bdini13/esp32-cc1101-multiband/output/placement-A2-top.png

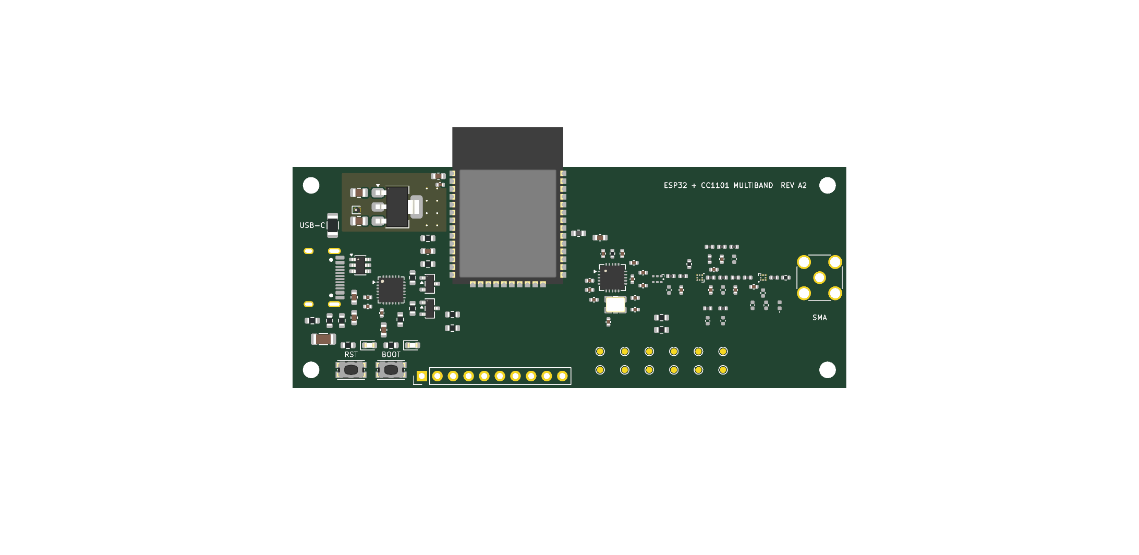
output/placement-A2-top.png
