bdini13/esp32-cc1101-multiband/output/placement-top.png

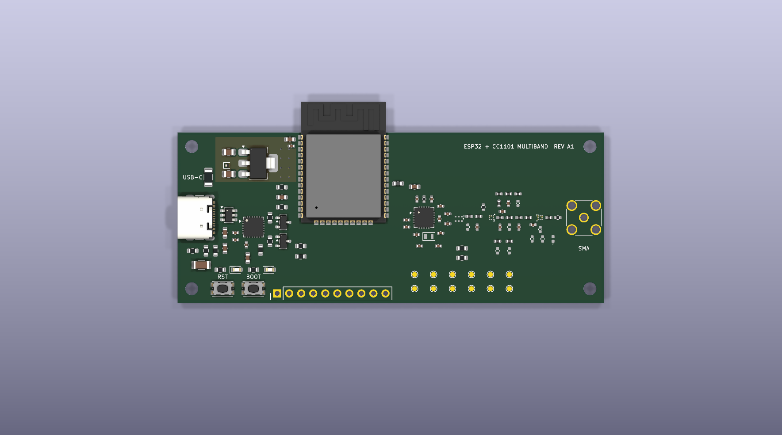
output/placement-top.png
